lmayencourt/faboy/pcb/original.png

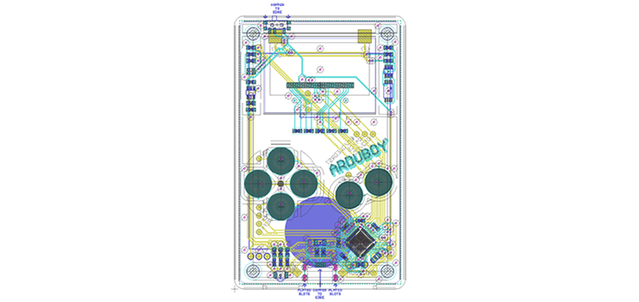
pcb/original.png
