lmayencourt/faboy/software/Qtboy/arduboy.png

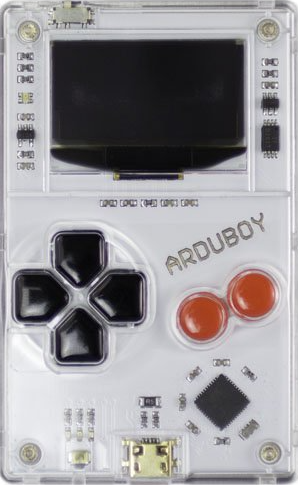
software/Qtboy/arduboy.png
