lmayencourt/faboy/software/game/ECOMD_AB_v10/ECOMD_AB_v10/Weapons.h

#ifndef WEAPONS_H
#define WEAPONS_H

#include <Arduino.h>

extern Arduboy arduboy;
extern SimpleButtons buttons;

#define POWERUP_MAXTIME     600
enum WEAPON_TYPE { DEFAULT_GUN = 0, SHOTGUN, MAGNUM, MACHINEGUN, FLAMETHROWER, DUAL_PISTOLS};
WEAPON_TYPE CURRENT_WEAPON;

PROGMEM const unsigned char guns[] = {
  // width, height
  16, 8,
  // tile 0
  0x00, 0x00, 0x00, 0x00, 0x7A, 0x7C, 0x2C, 0x1C, 0x0C, 0x0C,
  0x0C, 0x0C, 0x00, 0x00, 0x00, 0x00,
  // tile 1
  0x78, 0x78, 0x3A, 0x3C, 0x1C, 0x1C, 0x2C, 0x2C, 0x1C, 0x0C,
  0x0C, 0x1C, 0x1C, 0x1C, 0x1C, 0x0C,
  // tile 2
  0x00, 0xE0, 0xF0, 0x7A, 0x1C, 0x2E, 0x1A, 0x1A, 0x0E, 0x06,
  0x06, 0x06, 0x06, 0x06, 0x07, 0x00,
  // tile 3
  0x06, 0xCF, 0xFF, 0x3E, 0x2E, 0x1E, 0x0E, 0x0E, 0x1E, 0x7E,
  0xE6, 0x86, 0x06, 0x06, 0x07, 0x02,
  // tile 4
  0x62, 0x7A, 0x1E, 0x06, 0x0A, 0x06, 0x02, 0x02, 0xFA, 0xFE,
  0xFA, 0x02, 0x07, 0x07, 0x07, 0x07,
  // tile 5
  0x0C, 0x0C, 0x0C, 0x1C, 0x2C, 0x7C, 0x7A, 0x00, 0x00, 0x7A,
  0x7C, 0x2C, 0x1C, 0x0C, 0x0C, 0x0C,
};

PROGMEM const unsigned char bullets_is_mask[] = {
  // width, height
  16, 8,
  // frame 0
  0x04, 0x04, 0x00, 0x04, 0x00, 0x00, 0x00, 0x00, 0x00, 0x00,
  0x00, 0x00, 0x00, 0x00, 0x00, 0x00,
  // frame 1
  0x08, 0x00, 0x08, 0x14, 0x00, 0x00, 0x08, 0x00, 0x22, 0x00,
  0x08, 0x00, 0x00, 0x14, 0x00, 0x41,
  // frame 2
  0x04, 0x02, 0x04, 0x06, 0x00, 0x00, 0x00, 0x00, 0x00, 0x00,
  0x00, 0x00, 0x00, 0x00, 0x00, 0x00,
  // frame 3
  0x06, 0x06, 0x06, 0x00, 0x06, 0x00, 0x00, 0x00, 0x00, 0x00,
  0x00, 0x00, 0x00, 0x00, 0x00, 0x00,
  // frame 4
  0x08, 0x16, 0x11, 0x12, 0x0C, 0x00, 0x00, 0x00, 0x00, 0x00,
  0x00, 0x00, 0x00, 0x00, 0x00, 0x00,
  // frame 5
  0x04, 0x04, 0x04, 0x00, 0x00, 0x00, 0x00, 0x00, 0x00, 0x00,
  0x00, 0x00, 0x00, 0x00, 0x00, 0x00,
  // frame 6
  0x04, 0x00, 0x04, 0x04, 0x00, 0x00, 0x00, 0x00, 0x00, 0x00,
  0x00, 0x00, 0x00, 0x00, 0x00, 0x00,
  // frame 7
  0x41, 0x00, 0x14, 0x00, 0x00, 0x08, 0x00, 0x22, 0x00, 0x08,
  0x00, 0x00, 0x14, 0x08, 0x00, 0x08,
  // frame 8
  0x06, 0x04, 0x02, 0x04, 0x00, 0x00, 0x00, 0x00, 0x00, 0x00,
  0x00, 0x00, 0x00, 0x00, 0x00, 0x00,
  // frame 9
  0x06, 0x00, 0x06, 0x06, 0x06, 0x00, 0x00, 0x00, 0x00, 0x00,
  0x00, 0x00, 0x00, 0x00, 0x00, 0x00,
  // frame 10
  0x0C, 0x12, 0x11, 0x16, 0x08, 0x00, 0x00, 0x00, 0x00, 0x00,
  0x00, 0x00, 0x00, 0x00, 0x00, 0x00,
  // frame 11
  0x04, 0x04, 0x04, 0x00, 0x00, 0x00, 0x00, 0x00, 0x00, 0x00,
  0x00, 0x00, 0x00, 0x00, 0x00, 0x00,
};

class Bullet
{
  public:
    byte x;
    byte y;
    byte width = 4;
    byte height = 1;
    byte fuse = 0;
    byte xSpeed = 3;
    byte ySpeed = 0;
    byte damage = 1;
    boolean isActive = false;

    void Update() {
      if (isActive) {
        fuse--; if (fuse == 0) isActive = false;
        x += xSpeed;
        y += ySpeed;
      }
    }
};

class Weapons
{
  public:

    static const byte maxBullets = 6;
    int powerupTimer = POWERUP_MAXTIME;
    byte maxFuse = 23;
    byte fuse = 0;
    byte frameDelay = 1;
    byte maxCooldown =  3;
    byte kickBack = 0;
    byte cooldown = 0;
    byte currentBullet = 0;
    byte width = 4;
    byte height = 1;
    byte xSpeed = 3;
    byte xSpeedOffset = 0;
    byte yOffset = 0;
    byte ySpeed = 0;
    byte ySpeedOffset = 0;
    byte damage = 1;

    Bullet bullet[maxBullets];

    void shootDual()
    {
      currentBullet ++; if (currentBullet == maxBullets)currentBullet = 0;
      bullet[currentBullet].isActive = true;
      bullet[currentBullet].fuse =  maxFuse ;
      bullet[currentBullet].ySpeed = random(0, ySpeedOffset + 1);
      byte rand = random(0, 2); if (rand == 1) bullet[currentBullet].ySpeed *= -1;
    }
    boolean shoot()
    {
      if (cooldown == 0)
      {
        currentBullet ++; if (currentBullet == maxBullets)currentBullet = 0;
        bullet[currentBullet].isActive = true;
        bullet[currentBullet].fuse =  maxFuse ;
        bullet[currentBullet].ySpeed = random(0, ySpeedOffset + 1);
        byte rand = random(0, 2); if (rand == 1) bullet[currentBullet].ySpeed *= -1;

        cooldown = maxCooldown;
        return true;
      }
      else
      {
        return false;
      }
    }


    void Update()
    {

      //timer for weapons powerup (to avoid exploitation)
      powerupTimer --;
      
      if (cooldown > 0) cooldown --;

      for (byte i = 0; i < maxBullets; i++)
      {
        if (bullet[i].isActive)
        {
          bullet[i].Update();
        }
      }
    }

    void setBulletSpecs()
    {
      for (byte i = 0; i < maxBullets; i++)
      {
        bullet[i].width = width;
        bullet[i].height = height;
        bullet[i].xSpeed = xSpeed;
        bullet[i].ySpeed = ySpeed;
        bullet[i].damage = damage;
        bullet[i].isActive = false;
      }

    }

    void weaponSet(int weapType)
    {
      powerupTimer = POWERUP_MAXTIME;
      setBulletSpecs();
      switch (weapType) {
        case 0: //DEFAULT GUN
          frameDelay = 1;
          maxFuse = 30;
          fuse = 0;
          maxCooldown =  3;
          kickBack = 0;
          cooldown = 0;
          width = 4;
          height = 1;
          xSpeed = 3;
          xSpeedOffset = 0;
          yOffset = 0;
          ySpeed = 0;
          ySpeedOffset = 0;
          damage = 1;
          break;
        case 1: //SHOTGUN
          frameDelay = 1;
          maxFuse = 16;
          fuse = 0;
          maxCooldown =  40;
          kickBack = 8;
          cooldown = 0;
          width = 16;
          height = 7;
          xSpeed = 1;
          ySpeed = 0;
          yOffset = 0;
          ySpeedOffset = 0;
          damage = 5;
          break;
        case 2: //MAGNUM
          frameDelay = 1;
          maxFuse = 35;
          fuse = 0;
          maxCooldown =  20;
          kickBack = 4;
          cooldown = 0;
          width = 4;
          height = 2;
          xSpeed = 3;
          xSpeedOffset = 0;
          ySpeed = 0;
          yOffset = 0;
          ySpeedOffset = 0;
          damage = 2;
          break;
        case 3: //MACHINE_GUN:
          frameDelay = 1;
          maxFuse = 30;
          fuse = 0;
          maxCooldown =  8;
          kickBack = 5;
          cooldown = 0;
          width = 5;
          height = 2;
          xSpeed = 4;
          xSpeedOffset = 0;
          ySpeed = 0;
          yOffset = 1;
          ySpeedOffset = 0;
          damage = 1;
          break;
        case 4: //FLAMETHROWER:
          frameDelay = 3;
          maxFuse = 6;
          fuse = 0;
          maxCooldown =  4;
          cooldown = 0;
          kickBack = 0;
          width = 5;
          height = 5;
          xSpeed = 3;
          xSpeedOffset = 2;
          ySpeed = 0;
          yOffset = 1;
          ySpeedOffset = 1;
          damage = 2;
          break;
        case 5: //DUAL_PISTOLS:
          //SAME STATS AS DEFAULT_GUN
          frameDelay = 1;
          maxFuse = 30;
          fuse = 0;
          maxCooldown = 3;
          kickBack = 0;
          cooldown = 0;
          width = 3;
          height = 1;
          xSpeed = 3;
          xSpeedOffset = 0;
          yOffset = 0;
          ySpeed = 0;
          ySpeedOffset = 0;
          damage = 1;
          break;
      }
    }
};

Weapons weapon;

void makeShootingSounds() //pew pew sound
{
  switch (CURRENT_WEAPON)
  {
    case DEFAULT_GUN:
      arduboy.tunes.tone(100, 100);
      break;
    case SHOTGUN:
      arduboy.tunes.tone(140, 300);
      break;
    case MAGNUM:
      arduboy.tunes.tone(190, 300);
      break;
    case MACHINEGUN:
      arduboy.tunes.tone(120, 100);
      break;
    case FLAMETHROWER:
      arduboy.tunes.tone(100, 80);
      break;
    case DUAL_PISTOLS:
      arduboy.tunes.tone(100, 100);
      break;
  }
}

void shoot()
{
  if ((buttons.pressed(A_BUTTON) && CURRENT_WEAPON == MACHINEGUN)  || (buttons.pressed(A_BUTTON) && CURRENT_WEAPON == FLAMETHROWER) || buttons.justPressed(A_BUTTON))
  {
    //shoot normal bullets
    if (weapon.shoot()) {
      makeShootingSounds();
      byte yOffset = weapon.yOffset;
      byte randNum = random(0, 2); if (randNum == 1) yOffset *= -1;
      weapon.bullet[weapon.currentBullet].y = player.y + 2 + yOffset ;
      byte randxSpeedOffset = random(1, weapon.xSpeedOffset + 1);
      weapon.bullet[weapon.currentBullet].x = player.x + ((1 - (2 * playerFacing)) * 8);
      weapon.bullet[weapon.currentBullet].xSpeed =  ((1 - (2 * playerFacing)) * weapon.xSpeed) - ((1 - (2 * playerFacing)) * randxSpeedOffset);
      {
        for (byte i = 0; i <  weapon.kickBack; i++)
        {
          if (!checkCollisions()) player.x -= (1 - (2 * playerFacing));
        }
      }
      if (CURRENT_WEAPON == DUAL_PISTOLS)
      {
        weapon.shootDual();
        weapon.bullet[weapon.currentBullet].y = player.y + 3;
        weapon.bullet[weapon.currentBullet].x = player.x - ((-1 * playerFacing) * weapon.width);
        weapon.bullet[weapon.currentBullet].xSpeed = -  ((1 - (2 * playerFacing)) * weapon.xSpeed) + ((1 - (2 * playerFacing)));
      }
    }
  }
}

void updateWeapon()
{
  if (arduboy.everyXFrames(weapon.frameDelay))
  {
    weapon.Update();
    if (weapon.powerupTimer < 1)
    {
      CURRENT_WEAPON = DEFAULT_GUN;
      weapon.weaponSet(0);
    }
  }
}

void drawBullets()
{
  for (byte i = 0; i < weapon.maxBullets; i++)
  {
    if (weapon.bullet[i].isActive)  sprites.drawSelfMasked(weapon.bullet[i].x, weapon.bullet[i].y, bullets_is_mask, CURRENT_WEAPON + (playerFacing * 6));
  }
}

#endif
