lmayencourt/faboy/software/Faboy/src/core/core.cpp

#include "core.h"

// need to redeclare these here since we declare them static in .h
volatile uint8_t *ArduboyCore::mosiport, 
  *ArduboyCore::csport, *ArduboyCore::dcport;
uint8_t ArduboyCore::mosipinmask, 
  ArduboyCore::cspinmask, ArduboyCore::dcpinmask;

const uint8_t PROGMEM pinBootProgram[] = {
  // buttons
  PIN_LEFT_BUTTON, INPUT_PULLUP,
  PIN_RIGHT_BUTTON, INPUT_PULLUP,
  PIN_UP_BUTTON, INPUT_PULLUP,
  PIN_DOWN_BUTTON, INPUT_PULLUP,
  PIN_A_BUTTON, INPUT_PULLUP,
  PIN_B_BUTTON, INPUT_PULLUP,

  // OLED SPI
  DC, OUTPUT,
  CS, OUTPUT,
  RST, OUTPUT,
  0
};

const uint8_t PROGMEM lcdBootProgram[] = {
  // boot defaults are commented out but left here incase they
  // might prove useful for reference
  //
  // Further reading: https://www.adafruit.com/datasheets/SSD1306.pdf
  //
  // Display Off
  // 0xAE,     

  // Set Display Clock Divisor v = 0xF0
  // default is 0x80
  0xD5, 0xF0,

  // Set Multiplex Ratio v = 0x3F
  // 0xA8, 0x3F,   

  // Set Display Offset v = 0
  // 0xD3, 0x00, 

  // Set Start Line (0)
  // 0x40,     

  // Charge Pump Setting v = enable (0x14)
  // default is disabled
  0x8D, 0x14,   

  // Set Segment Re-map (A0) | (b0001)
  // default is (b0000)
  0xA1,     

  // Set COM Output Scan Direction
  0xC8,     

  // Set COM Pins v
  // 0xDA, 0x12,   

  // Set Contrast v = 0xCF
  0x81, 0xCF,   

  // Set Precharge = 0xF1
  0xD9, 0xF1,
    
  // Set VCom Detect
  // 0xDB, 0x40,   

  // Entire Display ON
  // 0xA4,     

  // Set normal/inverse display
  // 0xA6,  

  // Display On
  0xAF,     

  // set display mode = horizontal addressing mode (0x00)
  0x20, 0x00,  

  // set col address range 
  // 0x21, 0x00, COLUMN_ADDRESS_END,

  // set page address range
  // 0x22, 0x00, PAGE_ADDRESS_END
};


ArduboyCore::ArduboyCore() {}

void ArduboyCore::boot()
{
  #if F_CPU == 8000000L
  slowCPU();
  #endif

  SPI.begin();
  bootPins();
  bootLCD();

  #ifdef SAFE_MODE
  if (buttonsState() == (LEFT_BUTTON | UP_BUTTON))
    safeMode();
  #endif

  saveMuchPower();
}

#if F_CPU == 8000000L
// if we're compiling for 8Mhz we need to slow the CPU down because the
// hardware clock on the Arduboy is 16MHz
void ArduboyCore::slowCPU()
{
  uint8_t oldSREG = SREG;
  cli();                // suspend interrupts
  CLKPR = _BV(CLKPCE);  // allow reprogramming clock
  CLKPR = 1;            // set clock divisor to 2 (0b0001)
  SREG = oldSREG;       // restore interrupts
}
#endif

void ArduboyCore::bootPins()
{
  uint8_t pin, mode;
  const uint8_t *i = pinBootProgram;

  while(true) {
    pin = pgm_read_byte(i++);
    mode = pgm_read_byte(i++);
    if (pin==0) break;
    pinMode(pin, mode);
  }

  digitalWrite(RST, HIGH);
  delay(1);           // VDD (3.3V) goes high at start, lets just chill for a ms
  digitalWrite(RST, LOW);   // bring reset low
  delay(10);          // wait 10ms
  digitalWrite(RST, HIGH);  // bring out of reset
}

void ArduboyCore::bootLCD()
{
  // setup the ports we need to talk to the OLED
 // csport = portOutputRegister(digitalPinToPort(CS));
 // cspinmask = digitalPinToBitMask(CS);
 // dcport = portOutputRegister(digitalPinToPort(DC));
 // dcpinmask = digitalPinToBitMask(DC);
  pinMode(DC, OUTPUT);
  pinMode(CS, OUTPUT);

  SPI.setClockDivider(SPI_CLOCK_DIV2);

  LCDCommandMode();
  // run our customized boot-up command sequence against the
  // OLED to initialize it properly for Arduboy
  for (int8_t i=0; i < sizeof(lcdBootProgram); i++) {
    SPI.transfer(pgm_read_byte(lcdBootProgram + i));
  }
  LCDDataMode();
}

void ArduboyCore::LCDDataMode()
{
  //*dcport |= dcpinmask; // dc 1
  //*csport &= ~cspinmask;  // cs c0
  digitalWrite(DC, HIGH);
  digitalWrite(CS,LOW);

}

void ArduboyCore::LCDCommandMode()
{
 // *csport |= cspinmask;  
 // *dcport &= ~dcpinmask;
 // *csport &= ~cspinmask;

  digitalWrite(CS, HIGH);
  digitalWrite(DC, LOW);
  digitalWrite(CS, LOW);
}



void ArduboyCore::safeMode()
{
  blank(); // too avoid random gibberish
  while (true) {
    asm volatile("nop \n");
  }
}


/* Power Management */

void ArduboyCore::idle()
{
  set_sleep_mode(SLEEP_MODE_IDLE);
  sleep_mode();
}

void ArduboyCore::saveMuchPower()
{
  power_adc_disable();
  power_usart0_disable();
  power_twi_disable();
  // timer 0 is for millis()
  // timers 1 and 3 are for music and sounds
  power_timer2_disable();
  power_usart1_disable();
  // we need USB, for now (to allow triggered reboots to reprogram)
  // power_usb_disable()
}

uint8_t ArduboyCore::width() { return WIDTH; }

uint8_t ArduboyCore::height() { return HEIGHT; }


/* Drawing */

void ArduboyCore::paint8Pixels(uint8_t pixels)
{
  SPI.transfer(pixels);
}

void ArduboyCore::paintScreen(const unsigned char *image)
{
  for (int i = 0; i < (HEIGHT*WIDTH)/8; i++)
  {
    SPI.transfer(pgm_read_byte(image + i));
  }
}

// paint from a memory buffer, this should be FAST as it's likely what
// will be used by any buffer based subclass
void ArduboyCore::paintScreen(unsigned char image[])
{
  uint8_t c;
  int i = 0;

  SPDR = image[i++]; // set the first SPI data byte to get things started

  // the code to iterate the loop and get the next byte from the buffer is
  // executed while the previous byte is being sent out by the SPI controller
  while (i < (HEIGHT * WIDTH) / 8)
  {
    // get the next byte. It's put in a local variable so it can be sent as
    // as soon as possible after the sending of the previous byte has completed
    c = image[i++];

    while (!(SPSR & _BV(SPIF))) { } // wait for the previous byte to be sent

    // put the next byte in the SPI data register. The SPI controller will
    // clock it out while the loop continues and gets the next byte ready
    SPDR = c;
  }
  while (!(SPSR & _BV(SPIF))) { } // wait for the last byte to be sent
}

void ArduboyCore::blank()
{
  for (int i = 0; i < (HEIGHT*WIDTH)/8; i++)
    SPI.transfer(0x00);
}

void ArduboyCore::sendLCDCommand(uint8_t command)
{
  LCDCommandMode();
  SPI.transfer(command);
  LCDDataMode();
}

// invert the display or set to normal
// when inverted, a pixel set to 0 will be on
void ArduboyCore::invert(boolean inverse)
{
  sendLCDCommand(inverse ? OLED_PIXELS_INVERTED : OLED_PIXELS_NORMAL);
}

// turn all display pixels on, ignoring buffer contents
// or set to normal buffer display
void ArduboyCore::allPixelsOn(boolean on)
{
  sendLCDCommand(on ? OLED_ALL_PIXELS_ON : OLED_PIXELS_FROM_RAM);
}

// flip the display vertically or set to normal
void ArduboyCore::flipVertical(boolean flipped)
{
  sendLCDCommand(flipped ? OLED_VERTICAL_FLIPPED : OLED_VERTICAL_NORMAL);
}

#define OLED_HORIZ_FLIPPED 0xA0 // reversed segment re-map
#define OLED_HORIZ_NORMAL 0xA1 // normal segment re-map

// flip the display horizontally or set to normal
void ArduboyCore::flipHorizontal(boolean flipped)
{
  sendLCDCommand(flipped ? OLED_HORIZ_FLIPPED : OLED_HORIZ_NORMAL);
}

/* RGB LED */

void ArduboyCore::setRGBled(uint8_t red, uint8_t green, uint8_t blue)
{
#ifdef ARDUBOY_10 // RGB, all the pretty colors
  // inversion is necessary because these are common annode LEDs
  analogWrite(RED_LED, 255 - red);
  analogWrite(GREEN_LED, 255 - green);
  analogWrite(BLUE_LED, 255 - blue);
#elif defined(FABOY_DEV) // RGB, all the pretty colors
  // inversion is necessary because these are common annode LEDs
  analogWrite(RED_LED, 255 - red);
  analogWrite(GREEN_LED, 255 - green);
  analogWrite(BLUE_LED, 255 - blue);
#elif defined(AB_DEVKIT)
  // only blue on devkit
  digitalWrite(BLUE_LED, ~blue);
#endif
}

/* Buttons */

uint8_t ArduboyCore::getInput()
{
  return buttonsState();
}


uint8_t ArduboyCore::buttonsState()
{
  uint8_t buttons;
  
  // using ports here is ~100 bytes smaller than digitalRead()
#ifdef AB_DEVKIT
  // down, left, up
  buttons = ((~PINB) & B01110000);
  // right button
  buttons = buttons | (((~PINC) & B01000000) >> 4);
  // A and B
  buttons = buttons | (((~PINF) & B11000000) >> 6);
#elif defined(ARDUBOY_10)
  // down, up, left right
  buttons = ((~PINF) & B11110000);
  // A (left)
  buttons = buttons | (((~PINE) & B01000000) >> 3);
  // B (right)
  buttons = buttons | (((~PINB) & B00010000) >> 2);
  #elif defined(FABOY_DEV)
  // down, up, left right
  buttons = ((~PINF) & B00110011);
  // A (left), B(right)
  buttons = buttons | (((~PIND) & B00001100) );
#endif
  
  return buttons;
}
