lmayencourt/faboy/software/game/ECOMD_AB_v10/ECOMD_AB_v10/background.h

#ifndef BACKGROUND_H
#define BACKGROUND_H

byte fireFrame = 0;

PROGMEM const unsigned char surrounding_plus_mask[] = {
  // width, height
  8, 8,
  // tile 0
  0x00, 0x00, 0x00, 0x00, 0x00, 0x00, 0x00, 0x00, 0x00, 0x00,
  0x00, 0x00, 0x00, 0x00, 0x00, 0x00,
  // tile 1
  0xFF, 0xFF, 0xAA, 0xFF, 0x53, 0xFF, 0x02, 0xFF, 0x53, 0xFF,
  0x02, 0xFF, 0xFF, 0xFF, 0xFE, 0xFF,
  // tile 2
  0x03, 0x03, 0xF2, 0xF3, 0x13, 0xF3, 0x1E, 0xFF, 0x13, 0xF3,
  0x12, 0xF3, 0x13, 0xF3, 0x12, 0xF3,
  // tile 3
  0x13, 0xF3, 0x12, 0xF3, 0x13, 0xF3, 0x12, 0xF3, 0x13, 0xF3,
  0x12, 0xF3, 0x13, 0xF3, 0x12, 0xF3,
  // tile 4
  0x13, 0xF3, 0x12, 0xF3, 0x13, 0xF3, 0x1E, 0xFF, 0x13, 0xF3,
  0xF2, 0xF3, 0x03, 0x03, 0x02, 0x03,
  // tile 5
  0x03, 0x03, 0x02, 0x03, 0x03, 0x03, 0x02, 0x03, 0x03, 0x03,
  0x02, 0x03, 0x03, 0x03, 0x02, 0x03,
  // tile 6
  0x03, 0x03, 0x02, 0x03, 0xFF, 0xFF, 0x02, 0x03, 0x03, 0x03,
  0x02, 0x03, 0x03, 0x03, 0x02, 0x03,
  // tile 7
  0x03, 0x03, 0x02, 0x03, 0x03, 0x03, 0x02, 0x03, 0x03, 0x03,
  0x02, 0x03, 0xFF, 0xFF, 0x02, 0x03,
  // tile 8
  0xF3, 0xF3, 0x12, 0xF3, 0x1F, 0xFF, 0x12, 0xF3, 0x13, 0xF3,
  0x12, 0xF3, 0x13, 0xF3, 0x12, 0xF3,
  // tile 9
  0x13, 0xF3, 0x12, 0xF3, 0x13, 0xF3, 0x12, 0xF3, 0x1F, 0xFF,
  0x12, 0xF3, 0xF3, 0xF3, 0x02, 0x03,
  // tile 10
  0xFF, 0xFF, 0xAA, 0xFF, 0x00, 0xFF, 0x00, 0xFF, 0x00, 0xFF,
  0x00, 0xFF, 0xFF, 0xFF, 0xFF, 0xFF,
  // tile 11
  0xFF, 0xFF, 0xAA, 0xFF, 0x94, 0xFF, 0x80, 0xFF, 0x94, 0xFF,
  0x80, 0xFF, 0xFF, 0xFF, 0xFF, 0xFF,
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
0x00, 0x00, 0x00, 0x00, 0x00, 0x00, 0x80, 0x80, 0x00, 0x00, 0x00, 0x00, 0xE0, 0xE0, 0xC0, 0xC0, 
0x00, 0x00, 0x00, 0x00, 0x78, 0x78, 0xFE, 0xFE, 0xFC, 0xFC, 0x9E, 0xFE, 0xEF, 0xFF, 0xF1, 0xFF, 
0xFB, 0xFF, 0xF6, 0xFE, 0xEF, 0xFF, 0xF7, 0xFF, 0xCF, 0xFF, 0xFE, 0xFE, 0x7C, 0x7C, 0x01, 0x01, 

};


PROGMEM const byte backdrop_tiles[] =
{
  0,  0,  0,  0,  0,  0,  0,  0,  0,  0,  0,  0,  0, 14,  3,  8,  0,  0,  0,  0,
  0,  0,  7,  3,  7,  0,  0,  0,  0, 14, 15,  0,  0,  3,  3,  3,  0,  0,  0, 13,
  0,  4,  8,  3,  9, 10, 10, 13,  0,  3,  1, 13,  0,  3,  3,  3,  0,  7,  0,  2,
  1,  5,  3,  3,  3,  1,  1, 12, 11,  3,  3,  2, 10,  3,  3,  3,  5,  2,  0,  2,
  2,  6,  3,  3,  3, 11,  1,  3,  3,  3,  3,  2, 11,  3,  3,  3,  3,  3, 11,  2,
  3,  3,  3,  3,  3,  3,  3,  3,  3,  3,  3,  3,  3,  3,  3,  3,  3,  3,  3,  3,
};

void drawSurrounding()
{
  for (byte y = 0; y < 8; y++)
  {
    for (byte x = 0; x < 16; x++)
    {
      sprites.drawPlusMask(x * 8, y * 8, surrounding_plus_mask, pgm_read_byte(&surrounding_tiles[x + 16 * y]));
    }
  }
}

void drawBackDrop()
{
  for (byte y = 0; y < 6; y++)
  {
    for (byte x = 0; x < 20; x++)
    {
      sprites.drawPlusMask((x * 8) + 8 - (player.x / 4) , 16 + y * 8, backdrop_plus_mask, pgm_read_byte(&backdrop_tiles[x + 20 * y]));
    }
  }
}

void drawFirePit()
{
  if (arduboy.everyXFrames(2))fireFrame++;
  if (fireFrame > 14)fireFrame = 0;
  sprites.drawPlusMask(56, 48, firepit_plus_mask, fireFrame);
}
#endif
