lmayencourt/faboy/software/game/ECOMD_AB_v10/ECOMD_AB_v10/menu_bitmap.h

// TEAM-arg07b.png  width: 128 height: 48
const uint8_t PROGMEM TEAMarg2[] = {
0x7f,0x2f,0x30,0x68,0xb7,0xdb,0xed,0xdb,0x53,0x9f,0xfa,0x73,0x97,0xbb,0xd5,0xe7,
0x2e,0x77,0xb9,0xcb,0x5d,0x6e,0xbb,0xbd,0xdc,0xe5,0x2e,0x77,0xb9,0xcb,0x5d,0xee,
0x72,0x97,0x5b,0x2b,0xbb,0xdc,0x6e,0xb7,0xdb,0xed,0x76,0xbb,0xdd,0x6e,0xb7,0xdb,
0xed,0x76,0xbb,0xdd,0x6e,0xb7,0xca,0xae,0x43,0x57,0x76,0xbb,0x5d,0x6e,0xb7,0xdb,
0xed,0x76,0xbb,0xdd,0x6e,0xb7,0xdb,0xad,0xb2,0xdb,0x75,0xd8,0x5a,0x2a,0xb9,0xdd,
0x6e,0xb7,0xeb,0x75,0x74,0xd9,0xe5,0x72,0xf9,0xfd,0xdf,0xea,0x72,0x57,0x77,0x75,
0x97,0x3b,0x6d,0x95,0x93,0xca,0x2a,0xbb,0x0e,0xbf,0x6d,0x6f,0x75,0xab,0xed,0xb9,
0x5c,0x77,0x2a,0xcf,0x9f,0x76,0xda,0xd5,0xad,0x4e,0xf7,0xaa,0x57,0xe9,0x74,0x3a,
0x9d,0xbb,0xa4,0xc2,0xd1,0x76,0xb6,0xb4,0xd3,0x2e,0x9f,0x5e,0x5a,0x85,0xbc,0x74,
0x3a,0x9d,0x4e,0xa7,0x3b,0x67,0x57,0x5b,0xaf,0x93,0x4a,0xb9,0x9d,0x52,0xca,0x2d,
0x97,0xdb,0x74,0x6c,0x49,0xe5,0x9c,0x92,0x4a,0x2a,0xa9,0xa4,0x53,0x84,0xe9,0xf4,
0xea,0x53,0xbf,0x56,0x2a,0x65,0xed,0x6e,0xa7,0x94,0x52,0x4a,0x46,0x9f,0x5e,0xaf,
0x97,0xcb,0x6d,0xbc,0x4b,0xe7,0x5c,0xff,0x13,0x7a,0x9f,0xde,0xce,0xbe,0xd6,0xb9,
0xee,0xd4,0xae,0x3b,0xb5,0x6e,0x7b,0xab,0x5b,0x8d,0x24,0x25,0x4b,0x29,0x95,0x4a,
0x76,0x56,0x3a,0x1d,0xdb,0xce,0xcd,0x96,0x4e,0xa7,0xd3,0xe9,0xec,0x4e,0x4a,0xe9,
0xec,0x08,0xdb,0x3a,0x67,0xe7,0x52,0xb3,0x29,0x2d,0xf5,0xa8,0x4b,0xa7,0xd3,0xe9,
0x74,0xce,0xb9,0x5b,0x2f,0xdd,0x6a,0x87,0xac,0xa4,0x2a,0x25,0x95,0x54,0x52,0x49,
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
0x39,0xa9,0xf0,0xe8,0xf9,0x76,0x4e,0x75,0xce,0xa9,0xb4,0xbc,0x73,0xf2,0xae,0x96,
0x57,0xa5,0xaa,0x5a,0x9e,0x4e,0xa7,0xd3,0x4c,0xd2,0xb9,0x4b,0x2a,0xa9,0xa4,0x92,
0xca,0x6e,0xb7,0xdb,0xd0,0x99,0xb7,0x3e,0x34,0x66,0xd3,0xbb,0x4a,0x3a,0x9b,0x8f,
0x2e,0x7c,0xc5,0xd5,0x56,0x55,0xe5,0x94,0xba,0x5c,0xaf,0x2e,0x77,0xab,0xcb,0x49,
0x75,0x39,0xab,0xaa,0xda,0xaa,0x70,0xb7,0xde,0x2a,0xa9,0xa4,0x92,0xca,0x39,0x55,
0x4a,0x49,0x55,0x6a,0xab,0x4a,0x39,0x27,0x95,0x73,0x52,0x49,0xe7,0xe4,0x56,0xa9,
0x72,0x97,0xbb,0xdc,0xad,0x5c,0x27,0x63,0x5d,0x3a,0xe7,0x3a,0x97,0xea,0x9d,0x93,
0x4a,0x2a,0xa9,0xa4,0x72,0xce,0x71,0xd1,0xd9,0xab,0xda,0xae,0x6a,0xb9,0x54,0x72,
0xa9,0xe4,0x36,0x5f,0xb9,0xaa,0xea,0xaa,0xba,0xaa,0xae,0xaa,0xab,0xea,0xaa,0xca,
0x55,0xb6,0xb2,0x21,0x30,0x9d,0x4e,0xa7,0xd3,0xdb,0xed,0x76,0xab,0xa4,0xe2,0x92,
0x8a,0x34,0x45,0x54,0x55,0x11,0xc5,0xb5,0x8e,0x38,0xba,0x8a,0xac,0xaa,0x22,0xaa,
0x92,0xc1,0x63,0x9f,0x4a,0x11,0x55,0x55,0x7e,0xae,0xf5,0xbc,0xd1,0x55,0x64,0x55,
0x95,0xbf,0x72,0x63,0x2d,0xbf,0x2c,0xa5,0xa4,0x52,0xa5,0xa4,0x52,0xa5,0xa4,0x4a,
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
};
