lmayencourt/faboy/software/game/SHRUN-AB_v15/SHRUN-AB_v15/otherbitmaps.h

const unsigned char PROGMEM TEAMarg2[] = //128,48
{
  //         ########                                                                                       ########                 
  //         ###########                                                                                   ##      ##                
  //         ####    ##################                                                                   ##  #### ###               
  //         #### ##    ################ ####################           #############         ######     ##  ##  # ####              
  //         #### #####                #######################       ##################      ########   ##  ###  # #####             
  //         #### ##  ######  ######## ##                   ###     ####            ####     ##     ## ##  ####### #  ###            
  // ####### ####  #  ####### #####  #  # #################  ##    ###   ##########   ###   ##  ###  ###  ###  ### #   ### ##########
  //         ##### ##########  ####  ## #  ################# ##   ###  ##############   ##  ## #####  #  ###    ## ##  ###           
  //         ##### ########### ######## #   ################  #   ##  #################  ####  ######   ####    ## ########          
  // ##### # #####             ########     ################# #  ##  #######    ######## #### ######## ######  ### ########  # # ####
  // #  #    ###### ####################    ################# #  ## #######      #######  ##  #################### ########      #  #
  // #  # #  ###### ####################     #######          # ##  ######       ####  ## ## #################  ## ######## # #  #  #
  // ####    ######  #  ################     ##############   # ## #######       ####  ## #  #################  ## ########      ####
  // ####  # ####### #  #################  # ##############   ###  ######       ######### # ###################### ########  # # ####
  // ####    ####### ####################  # ###############  ### #######       ########    #####################  ########      ####
  // #### #   ######        #########      # ###############  ##  ######       #########   ###################### ######### # #  ####
  // ####     #####          ########     ##  ############## ### ######################    ###################### #########     #####
  // ##### #  #####          #########    ### ########        #  ######################   ####################### ########   #  #####
  // #####     ###            ########    ### ###############   ######################    ####################### ########      #####
  // ###### #  ###         #  #########  #### ################  #######      #########   ######## ############### ########  # # #####
  // ######    ##          #   ########  ####  ################  ######      ########    #######  ############### ########      #####
  // ####### #  #         ###  ######### ##### ################# #####       ########   ########   ###### ####### ######## # # ######
  // #######    #         ###   ########  #### #  ############## #####      ########    #######    #####  ####### ########     ######
  // ######## # ######## #####  ##  ##### #### #  ########                  ###  ###    #######     ###   ######  ########  #  ######
  // ########          # #####   #  ##### #### #####             #         ####  ##                 ##    ###  # #########     ######
  // #  ###### # # # # ########  #####    ####                ## #         ########           ##          ###  # ######### # # ###  #
  // #  ######          #######           ####                ## #     ###                     #            #### #########     ###  #
  // ########## # # # # #########         # ##                   #     ###             ##      ##             ## #########  # #######
  //                    ########         ## ##                   #    ####             ##       #                ########            
  //         ###         #######         #  ##              ######    ####            ####      ##  #    #       ########            
  // ######### ######    ######         ##   #       #####################            # ##       #  ##  ####      #######   #########
  //       ##   ##       ######         #    ################            ############## ######################     ######            
  //      ##     ##   ## #####         ## ## #########                   ############    #######################    #####            
  //     ## ##    ##  ##  ####         #  ##                                                  ##     #############   #### ##         
  //     #  ##     #      ###         ##          ########    ##########      #########       ##     ##### #########  ### ##         
  //     ##       ##      ###     #####          ##########   ###########    ###########           ######      ##########            
  //      ##   # ##       #############         ############  ############   ###########          ####            #######   ###      
  //       ##   ##   ###  ########  ####        ############  #####  #####  #####   ####       ## ####    ###               # #      
  //        ## ##    # #            ####        #####   ####  #####   ####  ####               ##  ##     # #               ###      
  //         ###     ###             ##         #####   ####  #####   ###   ####   ######                 ###                        
  //                                            ############  ##########    #####  ######                                            
  //                                            ###########      ########      ########                                              
  //                                            ########### #### ## ##### #### ######## ####                                         
  //                                            #####   ### #  # ##  #### #  # ######## #  #                                         
  //                                            #####   ### #### ##   ### #### ######## ####                                         
  //                                                                                                                                 
  //                                                                                                                                 
  //                                                                                                                                 
  0x40, 0x40, 0x40, 0x40, 0x40, 0x40, 0x40, 0x00, 0xFF, 0xFF, 0xFF, 0xFF, 0x83, 0x3B, 0xFB, 0x93, 0x96, 0xF6, 0xE6, 0xEC, 0xEC, 0xEC, 0xEC, 0xCC, 0x0C, 0x6C, 0xEC, 0xEC, 0xEC, 0xEC, 0x2C, 0x2C, 0xEC, 0x8C, 0x38, 0xF0, 0x18, 0x58, 0xD8, 0xD8, 0xD8, 0xD8, 0xD8, 0xD8, 0xD8, 0xD8, 0xD8, 0xD8, 0xD8, 0xD8, 0xD8, 0xD8, 0xD8, 0xD8, 0x98, 0x38, 0xF0, 0xE0, 0x00, 0x00, 0x00, 0x80, 0xC0, 0xE0, 0x70, 0x30, 0xB0, 0x98, 0xD8, 0xD8, 0xD8, 0xD8, 0xD8, 0xD8, 0xD8, 0xD8, 0xD8, 0xD8, 0x98, 0xB8, 0x30, 0x70, 0x60, 0xC0, 0x80, 0x00, 0x00, 0xC0, 0xF0, 0x38, 0x98, 0xD8, 0xD8, 0xD8, 0x98, 0x30, 0x60, 0xC0, 0x60, 0x30, 0x98, 0xCC, 0xE6, 0x73, 0x39, 0x3D, 0x65, 0xE5, 0xFD, 0x01, 0xFF, 0x9E, 0x1C, 0x38, 0xF0, 0xE0, 0xC0, 0x00, 0x40, 0x40, 0x40, 0x40, 0x40, 0x40, 0x40, 0x40, 0x40, 0x40, 
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
};

const unsigned char PROGMEM spotlight_bitmap[] =
{
  //                                 
  //                                 
  //             ########            
  //           ############          
  //         ################        
  //        ##################       
  //       ####################      
  //      ######################     
  //     ########################    
  //     ########################    
  //    ##########################   
  //    ##########################   
  //   ############################  
  //   ############################  
  //   ############################  
  //   ############################  
  //   ############################  
  //   ############################  
  //   ############################  
  //   ############################  
  //    ##########################   
  //    ##########################   
  //     ########################    
  //     ########################    
  //      ######################     
  //       ####################      
  //        ##################       
  //         ################        
  //           ############          
  //             ########            
  //                                 
  //                                 
  0x00, 0x00, 0x00, 0x00, 0x00, 0x80, 0xC0, 0xE0, 0xF0, 0xF0, 0xF8, 0xF8, 0xFC, 0xFC, 0xFC, 0xFC, 0xFC, 0xFC, 0xFC, 0xFC, 0xF8, 0xF8, 0xF0, 0xF0, 0xE0, 0xC0, 0x80, 0x00, 0x00, 0x00, 0x00, 0x00, 
  0x00, 0x00, 0xF0, 0xFC, 0xFF, 0xFF, 0xFF, 0xFF, 0xFF, 0xFF, 0xFF, 0xFF, 0xFF, 0xFF, 0xFF, 0xFF, 0xFF, 0xFF, 0xFF, 0xFF, 0xFF, 0xFF, 0xFF, 0xFF, 0xFF, 0xFF, 0xFF, 0xFF, 0xFC, 0xF0, 0x00, 0x00, 
  0x00, 0x00, 0x0F, 0x3F, 0xFF, 0xFF, 0xFF, 0xFF, 0xFF, 0xFF, 0xFF, 0xFF, 0xFF, 0xFF, 0xFF, 0xFF, 0xFF, 0xFF, 0xFF, 0xFF, 0xFF, 0xFF, 0xFF, 0xFF, 0xFF, 0xFF, 0xFF, 0xFF, 0x3F, 0x0F, 0x00, 0x00, 
  0x00, 0x00, 0x00, 0x00, 0x00, 0x01, 0x03, 0x07, 0x0F, 0x0F, 0x1F, 0x1F, 0x3F, 0x3F, 0x3F, 0x3F, 0x3F, 0x3F, 0x3F, 0x3F, 0x1F, 0x1F, 0x0F, 0x0F, 0x07, 0x03, 0x01, 0x00, 0x00, 0x00, 0x00, 0x00, 
};

const unsigned char PROGMEM shadowRunner_bitmap[] =
{
  //     # #     # #   # #       # # #       # # # # #               # # #         # #   # #   # #
  //    # # #   # #     # #     # # # #       # # # # # #         # # # # #       # #   # #     # #
  //   # # #     # #   # #     # # # # #     # # # # # # #       # # # # # #       # #   # #   # #
  //  # # # #   # #     # #   # # # # # #     # # # # # # #     # # # # # # #     # #   # #     # #
  //   # #       # #   # #     # #     # #   # #       # #       # #     # # #     # #   # #   # #
  //  # # #     # #     # #   # #     # #     # #       # #     # #       # # #   # #   # #     # #
  //   # #       # # # # #     # #     # #   # #         # #   # #         # #     # #   # #   # #
  //  # # #     # # # # # #   # #     # #     # #       # #     # #         # #   # #   # #     # #
  //   # # #     # # # # #     # # # # # #   # #         # #   # #         # #     # #   # #   # #
  //    # # #   # # # # # #   # # # # # #     # #       # #     # #         # #   # #   # #     # #
  //     # #     # #   # #     # # # # # #   # #       # # #   # # #       # #     # #   # #   # #
  //    # # #   # #     # #   # # #   # #     # # # # # # #     # # #     # #     # #   # #     # #
  // # # # #     # #   # #     # #           #           #       # #         #       #         # #
  //  # # #     # #     # #   # #    ######   # ###  ###    ####  #   #####    #####   ######   # #
  // # # #       # #   # #     # #   #######    ###  ###   ######    #######  ###### # #######   #
  //  # #       # #     # #   # #    ######## # ###  ###  ########  ########  ######   ########
  //                                 ###  ###   ###  ###  ###  ###  ###  ###  ###      ###  ###
  //                                 ###  ###   ###  ###  ###  ###  ###  ###  ######   ###  ###
  //                                 ### ####   ###  ###  ###  ###  ###  ###  ######   ### ####
  //                                 ### ###    ###  ###  ###  ###  ###  ###  ######   ### ###
  //                                 ### ###    ###  ###  ###  ###  ###  ###  ###      ### ###
  //                                 ### ####   ########  ###  ###  ###  ###  ######   ### ####
  //                                 ###  ###    ######   ###  ###  ###  ###  ######   ###  ###
  //
  0x00, 0xA8, 0x54, 0xAA, 0x55, 0xAA, 0x05, 0x0A, 0x00, 0x00, 0x00, 0xAA, 0x55, 0xAA, 0x55, 0x80, 0x40, 0x80, 0x55, 0xAA, 0x55, 0xAA, 0x00, 0x00, 0x00, 0xA8, 0x54, 0xAA, 0x55, 0x0A, 0x05, 0x0A, 0x05, 0xAA, 0x54, 0xA8, 0x50, 0x00, 0x00, 0x00, 0x55, 0xAA, 0x55, 0xAA, 0x05, 0x0A, 0x05, 0x0A, 0x05, 0x0A, 0x14, 0xAA, 0x54, 0xA8, 0x40, 0x00, 0x00, 0x00, 0x40, 0xA8, 0x54, 0xAA, 0x14, 0x0A, 0x05, 0x0A, 0x05, 0x0A, 0x15, 0x2A, 0x54, 0xA8, 0x50, 0xA0, 0x00, 0x00, 0x00, 0xAA, 0x55, 0xAA, 0x55, 0x00, 0x00, 0xAA, 0x55, 0xAA, 0x55, 0x00, 0x00, 0x00, 0x55, 0xAA, 0x55, 0xAA,
  0x50, 0xA0, 0x51, 0xAA, 0x55, 0x2A, 0x15, 0x0A, 0x00, 0x00, 0x00, 0xAA, 0x55, 0xAA, 0x55, 0x02, 0x01, 0x02, 0x55, 0xAA, 0x55, 0xAA, 0x00, 0x00, 0x00, 0xAA, 0x55, 0xAA, 0x55, 0x0A, 0x05, 0x02, 0xE5, 0xEA, 0xE5, 0xEA, 0xE5, 0xE0, 0xC0, 0x80, 0x15, 0xAA, 0x05, 0xEA, 0xE0, 0xE8, 0x00, 0x08, 0xE0, 0xE8, 0xE4, 0x0A, 0x15, 0x8A, 0xC5, 0xE0, 0xE0, 0xE0, 0xE5, 0xCA, 0x95, 0x2A, 0x14, 0x88, 0xC0, 0xE0, 0xE0, 0xE0, 0xE0, 0xE8, 0xC5, 0x0A, 0x15, 0xC2, 0xE0, 0xE0, 0xE0, 0xEA, 0xE5, 0x0A, 0x55, 0x00, 0xE0, 0xEA, 0xE5, 0xEA, 0xE5, 0xE0, 0xC0, 0x80, 0x15, 0x2A, 0x55, 0x2A,
  0x00, 0x00, 0x00, 0x00, 0x00, 0x00, 0x00, 0x00, 0x00, 0x00, 0x00, 0x00, 0x00, 0x00, 0x00, 0x00, 0x00, 0x00, 0x00, 0x00, 0x00, 0x00, 0x00, 0x00, 0x00, 0x00, 0x00, 0x00, 0x00, 0x00, 0x00, 0x00, 0x7F, 0x7F, 0x7F, 0x00, 0x3C, 0x7F, 0x7F, 0x67, 0x00, 0x00, 0x00, 0x3F, 0x7F, 0x7F, 0x60, 0x60, 0x7F, 0x7F, 0x3F, 0x00, 0x00, 0x7F, 0x7F, 0x7F, 0x00, 0x00, 0x7F, 0x7F, 0x7F, 0x00, 0x00, 0x7F, 0x7F, 0x7F, 0x00, 0x00, 0x7F, 0x7F, 0x7F, 0x00, 0x00, 0x7F, 0x7F, 0x7F, 0x6E, 0x6E, 0x6E, 0x00, 0x00, 0x00, 0x7F, 0x7F, 0x7F, 0x00, 0x3C, 0x7F, 0x7F, 0x67, 0x00, 0x00, 0x00, 0x00,
};


const unsigned char PROGMEM menu_bitmap[] =
{
  //
  // ## ##  ### ##    ###
  // ## ## #### ##   #####
  // ##### ##   ##   ## ##
  // ##### #### ##   #####
  // ## ## ##   ##   ####
  // ## ## #### #### ##
  // ## ##  ###  ### ##
  //
  // ##   ###   ####  ####
  // ##  ##### ####  ######
  // ##  ## ## ##   ###  ###
  // ##  ## ## ###  ##    ##
  // ##  ## ## ###  ###  ###
  // ##  ## ## ##    ######
  // ##  ## ## ##     ####
  //
  //  ###   ####   ## ##  ###  ####
  // ####  ######  ## ## ##### #####
  // ##   ###  ### ## ## ## ## ##  ##
  //  ##  ##    ## ## ## ## ## ##  ##
  //   ## ###  ### ## ## ## ## ##  ##
  // ####  ######  ##### ## ## #####
  // ###    ####    ###  ## ## ####
  //
  //  ###  ##    ###  ##  ##
  // ##### ##   #####  ####
  // ## ## ##   ## ##   ##
  // ##### ##   #####   ##
  // ####  ##   #####   ##
  // ##    #### ## ##   ##
  // ##     ### ## ##   ##
  0xFE, 0xFE, 0x18, 0xFE, 0xFE, 0x00, 0x7C, 0xFE, 0xD6, 0xD6, 0x00, 0x7E, 0xFE, 0xC0, 0xC0, 0x00, 0xFC, 0xFE, 0x36, 0x3E, 0x1C, 0x00, 0x00, 0x00, 0x00, 0x00, 0x00, 0x00, 0x00, 0x00, 0x00, 0x00,
  0xFE, 0xFE, 0x00, 0x00, 0xFC, 0xFE, 0x06, 0xFE, 0xFC, 0x00, 0xFC, 0xFE, 0x36, 0x06, 0x02, 0x38, 0x7C, 0xEE, 0xC6, 0xC6, 0xEE, 0x7C, 0x38, 0x00, 0x00, 0x00, 0x00, 0x00, 0x00, 0x00, 0x00, 0x00,
  0xCC, 0xDE, 0xF6, 0x66, 0x00, 0x38, 0x7C, 0xEE, 0xC6, 0xC6, 0xEE, 0x7C, 0x38, 0x00, 0x7E, 0xFE, 0xC0, 0xFE, 0x7E, 0x00, 0xFC, 0xFE, 0x06, 0xFE, 0xFC, 0x00, 0xFE, 0xFE, 0xC6, 0xC6, 0x7C, 0x38,
  0xFC, 0xFE, 0x36, 0x3E, 0x1C, 0x00, 0x7E, 0xFE, 0xC0, 0xC0, 0x00, 0xFC, 0xFE, 0x36, 0xFE, 0xFC, 0x00, 0x02, 0x06, 0xFC, 0xFC, 0x06, 0x02, 0x00, 0x00, 0x00, 0x00, 0x00, 0x00, 0x00, 0x00, 0x00,
};

const unsigned char PROGMEM yes_bitmap[] =
{
  //
  // ##  ##  ###  ###
  //  ####  #### ####
  //   ##   ##   ##
  //   ##   ####  ##
  //   ##   ##     ##
  //   ##   #### ####
  //   ##    ### ###
  0x02, 0x06, 0xFC, 0xFC, 0x06, 0x02, 0x00, 0x7C, 0xFE, 0xD6, 0xD6, 0x00, 0xCC, 0xDE, 0xF6, 0x66,
};

const unsigned char PROGMEM no_bitmap[] =
{
  //
  //  ###    ####
  // #####  ######
  // ## ## ###  ###
  // ## ## ##    ##
  // ## ## ###  ###
  // ## ##  ######
  // ## ##   ####
  0xFC, 0xFE, 0x06, 0xFE, 0xFC, 0x00, 0x38, 0x7C, 0xEE, 0xC6, 0xC6, 0xEE, 0x7C, 0x38,
};


const unsigned char PROGMEM shade_bitmap[] =
{
  //  # # # # # # # # # # # # # # # #
  // # # # # # # # # # # # # # # # #
  //  # # # # # # # # # # # # # # # #
  // # # # # # # # # # # # # # # # #
  //  # # # # # # # # # # # # # # # #
  // # # # # # # # # # # # # # # # #
  //  # # # # # # # # # # # # # # # #
  // # # # # # # # # # # # # # # # #
  0xAA, 0x55, 0xAA, 0x55, 0xAA, 0x55, 0xAA, 0x55, 0xAA, 0x55, 0xAA, 0x55, 0xAA, 0x55, 0xAA, 0x55, 0xAA, 0x55, 0xAA, 0x55, 0xAA, 0x55, 0xAA, 0x55, 0xAA, 0x55, 0xAA, 0x55, 0xAA, 0x55, 0xAA, 0x55,
};


const unsigned char PROGMEM info_bitmap[] =
{
  //                                                                                                 
  //                                               ##               ##    #####     #####  #####   ##
  //                                               ##               ##   #######   ######  ######  ##
  //   ####     ####    ####    ######    ####     #####   ## ##    ##  ###   ###     ##   ##  ##  ##
  //  ######   ######  ######  ########  ######    ######  ## ##    ##  ##     ##   #####  ## ###  ##
  //  ##  ##   ##  ##  ##  ##  ## ## ##  ## ###    ##  ##  ## ##    ##  ##     ##      ##  ## ##   ##
  //  ##  ##   ##  ##  ##  ##  ## ## ##  ##        ##  ##  ## ##    ##  ###   ###      ##  ## ###  ##
  //  ######   ######  ######  ## ## ##  #####     ######  #####   ###   #######   ######  ##  ##  ##
  //   #####    #####   #####  ## ## ##   ####      ####    ####   ##     #####     ####   ##  ### ##
  //            #  ##                                        ###                                     
  //             ###                                       ####                                      
  //             ###                                       ###                                       
  //                                                                                                 
  //                 ##    ##       ##    ##               ##             ##                     ##  
  //                 ##    ##       ##    ##               ##             ##                    ###  
  //   ## ## ##  ##  ###   ####     ###   ####    ####     ####    ####   ##   ####      ####   ##   
  //   ## ## ##  ##  ###   #####    ###   #####  ######    #####  ######  ##  ######    ######  ##   
  //   ## ## ##  ##  ##    ## ##    ##    ## ##  ## ###    ## ##  ## ###  ##  ##  ##    ##  ##  ###  
  //   ## ## ##  ##  ####  ## ##    ####  ## ##  ##        ## ##  ##      ##  ##  ##    ##  ##  ###  
  //   ########  ##   ###  ## ##     ###  ## ##  #####     ## ##  #####   ##  ######    ######  ##   
  //    ######   ##    ##  ## ##      ##  ## ##   ####     ## ##   ####   ##  ####       ####   ##   
  //                                                                          ##                     
  //                            ######                  ##                    ##                     
  //                            ######                  ##                                           
  //                              ##    ##   ####     ####   ####     ##   ##                        
  //                              ##   ###  ######  ######  ######   ###  ###                        
  //                              ##   ##   ##  ##  ##  ##  ##  ##   ###  ###                        
  //                              ##   ##   ##  ##  ##  ##  ##  ##   ##   ##                         
  //                              ##   ##   ######  ######  ######  ###  ###                         
  //                              ##   ##    ####    ####    ####   ##   ##                          
  //                                                                                                 
  //                    ######                                                ####                   
  //                    #######                                               ####                   
  //                    ##   ###   ##   ####    ####    ######    ####    ##   ##                    
  //                    ##    ##  ###  ######  ######  ########  ######  ###  ####                   
  //                    ##    ##  ##   ## ###  ##  ##  ## ## ##  ## ###  ##     ##                   
  //                    ##   ###  ##   ##      ##  ##  ## ## ##  ##      ##     ##                   
  //                    ## ####   ##   #####   ######  ## ## ##  #####   ##   ####                   
  //                    ## ###    ##    ####    #####  ## ## ##   ####   ##   ###                    
  //                                                                                                 
  0x00, 0xF0, 0xF8, 0x98, 0x98, 0xF8, 0xF0, 0x00, 0x00, 0x00, 0xF0, 0xF8, 0x98, 0x98, 0xF8, 0xF0, 0x00, 0x00, 0xF0, 0xF8, 0x98, 0x98, 0xF8, 0xF0, 0x00, 0x00, 0xF0, 0xF8, 0x18, 0xF8, 0xF8, 0x18, 0xF8, 0xF0, 0x00, 0x00, 0xF0, 0xF8, 0x98, 0xB8, 0xB8, 0x30, 0x00, 0x00, 0x00, 0x00, 0xFE, 0xFE, 0x98, 0x98, 0xF8, 0xF0, 0x00, 0x00, 0xF8, 0xF8, 0x80, 0xF8, 0xF8, 0x00, 0x00, 0x00, 0x80, 0xFE, 0xFE, 0x00, 0x00, 0x78, 0xFC, 0xCE, 0x86, 0x86, 0x86, 0xCE, 0xFC, 0x78, 0x00, 0x00, 0x84, 0x96, 0x96, 0x9E, 0xFE, 0xF6, 0x00, 0x00, 0xFE, 0xFE, 0x06, 0x76, 0xFE, 0xDC, 0x00, 0x00, 0xFE, 0xFE, 
  0x00, 0x00, 0x81, 0x81, 0x01, 0x81, 0x81, 0x00, 0x80, 0x80, 0x00, 0x03, 0x8D, 0x8D, 0x0F, 0x03, 0xE0, 0xE0, 0x80, 0x01, 0x01, 0x01, 0xE1, 0xE1, 0x80, 0x80, 0x01, 0x01, 0x00, 0x01, 0x01, 0xE0, 0xE1, 0x81, 0x00, 0x00, 0x00, 0xE1, 0xE1, 0x81, 0x81, 0x00, 0x00, 0x00, 0x00, 0x80, 0x80, 0x81, 0x81, 0x01, 0x01, 0x00, 0x00, 0x00, 0xEC, 0xED, 0x8F, 0x87, 0x03, 0x00, 0x00, 0x00, 0x81, 0x81, 0x80, 0x80, 0x00, 0x00, 0x00, 0xE1, 0xE1, 0x01, 0x01, 0x01, 0x80, 0x80, 0x80, 0x80, 0x00, 0x01, 0x01, 0x01, 0x01, 0x00, 0x80, 0x80, 0x81, 0x81, 0x00, 0x00, 0x01, 0xC1, 0xE1, 0x60, 0x01, 0x01, 
  0x00, 0x00, 0x0F, 0x1F, 0x18, 0x1F, 0x1F, 0x18, 0x1F, 0x0F, 0x00, 0x00, 0x1F, 0x1F, 0x00, 0x00, 0x07, 0x0F, 0x1D, 0x1C, 0x00, 0x00, 0x1F, 0x1F, 0x01, 0x1F, 0x1F, 0xC0, 0xC0, 0xC0, 0xC0, 0xC7, 0xCF, 0x1D, 0x1C, 0x00, 0x00, 0x1F, 0x1F, 0x01, 0x1F, 0x1F, 0x00, 0x00, 0x0F, 0x1F, 0x19, 0x1B, 0x1B, 0x03, 0x00, 0xC0, 0xC0, 0x00, 0x1F, 0x1F, 0x01, 0x1F, 0x1F, 0x00, 0x00, 0x0F, 0x1F, 0x19, 0x1B, 0x1B, 0x03, 0x00, 0x00, 0x1F, 0x1F, 0x00, 0x00, 0x7F, 0x7F, 0x19, 0x19, 0x0F, 0x0F, 0x00, 0x00, 0x00, 0x00, 0x0F, 0x1F, 0x19, 0x19, 0x1F, 0x0F, 0x00, 0x00, 0x1F, 0x1F, 0x06, 0x00, 0x00, 
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
};


const unsigned char PROGMEM pause_bitmap[] =
{
  //
  //     # #         # # #     # #   # #       # #     # # #
  //    # # #       # # # #   # #     # #     # #     # # # #
  //   # # # #     # # # #     # #   # #     # # #   # # # #
  //  # # # # #   # # # # #   # #     # #   # # #   # # # # #
  // # #     # # # #     # #   # #   # #     # #     # #
  //  # #   # #   # #   # #   # #     # #   # # #   # #
  // # #   # # # # #     # #   # #   # #     # #     # # # #
  //  # # # # #   # #   # #   # #     # #   # # #   # # # #
  // #### #####  ###### ####  ####   ####    #####  ########
  // #### ####   ###### ####  ####   ####    #####  ########
  // ####        ###### ####  ####   ####    #####  ####
  // ####        ###### ####  ###########   ######  #########
  // ####        ####   ####   #########   ######    ########
  // ####        ####   ####    #######    ######     #######
  // ####        ####   ####     #####     ####        #####
  0xA0, 0x50, 0xA8, 0x54, 0x0A, 0x14, 0x8A, 0x54, 0xA8, 0x50, 0xA0, 0x00, 0xA0, 0x50, 0xA8, 0x54, 0x0A, 0x14, 0x0A, 0x54, 0xAA, 0x54, 0xA0, 0x00, 0x00, 0x54, 0xAA, 0x54, 0xAA, 0x00, 0x00, 0x00, 0xAA, 0x54, 0xAA, 0x54, 0x00, 0x00, 0x00, 0x50, 0xA8, 0x54, 0xAA, 0x54, 0x0A, 0x00, 0x00, 0x50, 0xA8, 0x54, 0xAA, 0x14, 0x8A, 0x14, 0x8A, 0x14,
  0xFE, 0xFF, 0xFE, 0xFF, 0x00, 0x07, 0x06, 0x07, 0x06, 0x03, 0x00, 0x00, 0xFE, 0xFF, 0xFE, 0xFF, 0x1E, 0x1E, 0x00, 0xFF, 0xFE, 0xFF, 0xFE, 0x00, 0x00, 0x1F, 0x3E, 0x7F, 0xFE, 0xF0, 0xF0, 0xF0, 0xFE, 0x7F, 0x3E, 0x1F, 0x00, 0x00, 0xE0, 0xF1, 0xFE, 0xFF, 0x7E, 0x7F, 0x1E, 0x00, 0x00, 0x1F, 0x3E, 0x7F, 0xFE, 0xF7, 0xF6, 0xF7, 0xF6, 0x70,
};

const unsigned char PROGMEM gameover_bitmap[] =
{
  //
  //          # # #         # # #       # # #   # # #       # # #
  //       # # # #         # # # #     # # # # # # # #     # # # #
  //      # # # # #       # # # # #   # # # # # # # # #   # # # #
  //     # # # # #       # # # # # #   # # # # # # # #   # # # # #
  //      # #     #     # # #   # #   # #   # #     # #   # #
  //     # #             # #     # #   # #   # #   # #   # #
  //    # #             # #     # #   # #   # #     # #   # # # #
  //     # #     # #     # #     # #   # #   # #   # #   # # # # #
  //    # #     # # #   # # #   # #   # #   # #     # #   # # # #
  //     # #     # # #   # # #   # #   # #   # #   # #   # # # # #
  //    # # #   # # #   # # #   # #
  //     # # #     # #   # # #   #  #####   ### ###  ### #####
  //      # # # # # #   # #     #  #######  ######  #### ###### #
  //       # # # # #     # #      ###   ###  #####  ##   ##  ##  #
  //        # # # #     # #     # ##  #  ##  ####   #### ## ### #
  //         # # #       # #      ##     ##  ####   #### ## ##   #
  //                              ###   ###   ##    ##   ## ###
  //                               #######    ##    #### ##  ##
  //                                #####     #      ### ##  ###
  //
  //
  //
  //
  0x00, 0x00, 0x00, 0x80, 0x50, 0xA8, 0x54, 0x28, 0x14, 0x0A, 0x14, 0x0A, 0x14, 0x2A, 0x00, 0x00, 0x00, 0x00, 0x00, 0xA0, 0x50, 0xA8, 0x54, 0x2A, 0x14, 0x0A, 0x14, 0xAA, 0x54, 0xA8, 0x50, 0x00, 0x00, 0xA8, 0x54, 0xAA, 0x54, 0x0A, 0x14, 0xAA, 0x54, 0xA8, 0x54, 0x0A, 0x14, 0x0A, 0x54, 0xAA, 0x54, 0xA8, 0x00, 0x00, 0x50, 0xA8, 0x54, 0xAA, 0x14, 0x8A, 0x14, 0x8A, 0x14, 0x00, 0x00, 0x00,
  0x00, 0x00, 0x00, 0x0A, 0x15, 0x2A, 0x55, 0xA8, 0x50, 0xA0, 0x40, 0xAA, 0x45, 0xAA, 0x55, 0x2A, 0x14, 0x00, 0x00, 0xAA, 0x55, 0xAA, 0x55, 0x0A, 0x14, 0x00, 0x00, 0xAA, 0x15, 0xCA, 0xE5, 0x70, 0x30, 0xB2, 0x35, 0x72, 0xE5, 0xC0, 0x00, 0x32, 0xF5, 0xF2, 0xE5, 0xF0, 0x70, 0x10, 0x05, 0xE2, 0xF5, 0xB2, 0xB0, 0x00, 0xF5, 0xF2, 0x35, 0xB2, 0xF5, 0xE2, 0x05, 0xA2, 0x45, 0x00, 0x00, 0x00,
  0x00, 0x00, 0x00, 0x00, 0x00, 0x00, 0x00, 0x00, 0x01, 0x00, 0x01, 0x00, 0x01, 0x00, 0x00, 0x00, 0x00, 0x00, 0x00, 0x00, 0x01, 0x00, 0x01, 0x00, 0x00, 0x00, 0x00, 0x00, 0x00, 0x03, 0x07, 0x0E, 0x0C, 0x0C, 0x0C, 0x0E, 0x07, 0x03, 0x00, 0x00, 0x01, 0x0F, 0x07, 0x01, 0x00, 0x00, 0x00, 0x07, 0x0F, 0x0D, 0x0D, 0x00, 0x0F, 0x0F, 0x00, 0x03, 0x0F, 0x0E, 0x08, 0x00, 0x01, 0x00, 0x00, 0x00,
};

const unsigned char PROGMEM score_bitmap[] =
{
  //
  //    #### #### #### ###  ####
  //    #    #    #  # #  # #    #
  //    #### #    #  # #  # ##
  //       # #    #  # ###  #
  //    #### #### #### #  # #### #
  //    #### #### #### #  # #### #
  //
  0x00, 0x00, 0x00, 0x6E, 0x6A, 0x6A, 0x7A, 0x00, 0x7E, 0x62, 0x62, 0x62, 0x00, 0x7E, 0x62, 0x62, 0x7E, 0x00, 0x7E, 0x12, 0x12, 0x6C, 0x00, 0x7E, 0x6A, 0x62, 0x62, 0x00, 0x64, 0x00, 0x00, 0x00,
};

const unsigned char PROGMEM candletip_bitmap[] =
{
  //           ####
  //       ## ######
  //    ############
  //   #############
  //  ##############
  // ###############
  // ###############
  // ###############
  // ###############
  // ###############
  // ###############
  // # #############
  // # #############
  // # #############
  // # #############
  //   #############
  //   #############
  //   ############
  //   ############
  //   ############
  //   ############
  //   ############
  //   ############
  //   ############
  //   ############
  //   ############
  //   ############
  //   ############
  //   ############
  //   ############
  //   ############
  //   ############
  0xE0, 0xF0, 0xF8, 0xFC, 0xFC, 0xFC, 0xFE, 0xFE, 0xFC, 0xFE, 0xFF, 0xFF, 0xFF, 0xFF, 0xFE, 0x00,
  0x7F, 0x07, 0xFF, 0xFF, 0xFF, 0xFF, 0xFF, 0xFF, 0xFF, 0xFF, 0xFF, 0xFF, 0xFF, 0xFF, 0xFF, 0x00,
  0x00, 0x00, 0xFF, 0xFF, 0xFF, 0xFF, 0xFF, 0xFF, 0xFF, 0xFF, 0xFF, 0xFF, 0xFF, 0xFF, 0x01, 0x00,
  0x00, 0x00, 0xFF, 0xFF, 0xFF, 0xFF, 0xFF, 0xFF, 0xFF, 0xFF, 0xFF, 0xFF, 0xFF, 0xFF, 0x00, 0x00,
};

const unsigned char PROGMEM life_bitmap[] =
{
  //        #    # #### ####
  //   #### #    # #    #
  //   #    #    # ###  ####
  // #####  #    # #    #
  //  ###   #### # #    ####
  //   #    #### # #    ####
  0x08, 0x18, 0x3E, 0x1A, 0x0A, 0x02, 0x00, 0x3F, 0x30, 0x30, 0x30, 0x00, 0x3F, 0x00, 0x3F, 0x05, 0x05, 0x01, 0x00, 0x3F, 0x35, 0x35, 0x35, 0x00,
};
