lmayencourt/faboy/software/game/ECOMD_AB_v10/ECOMD_AB_v10/score.h

#ifndef SCORE_H
#define SCORE_H


//define score font size
#define SCORE_SMALL_FONT          0
#define SCORE_BIG_FONT            1

PROGMEM const unsigned char numbersSmall[] = {
// width, height
3, 8,
// frame 0
0x1F, 0x11, 0x1F, 
// frame 1
0x12, 0x1F, 0x10, 
// frame 2
0x1D, 0x15, 0x17, 
// frame 3
0x11, 0x15, 0x1F, 
// frame 4
0x07, 0x04, 0x1F, 
// frame 5
0x17, 0x15, 0x1D, 
// frame 6
0x1F, 0x15, 0x1D, 
// frame 7
0x01, 0x01, 0x1F, 
// frame 8
0x1F, 0x15, 0x1F, 
// frame 9
0x17, 0x15, 0x1F, 
};


PROGMEM const unsigned char numbersBig[] = {
// width, height
18, 32,
// frame 0
0x40, 0xE0, 0x98, 0xFC, 0xFC, 0xF4, 0x1C, 0x1C, 0x14, 0x14, 
0x7C, 0xF4, 0xFE, 0xF5, 0xD8, 0x08, 0x00, 0x00, 0x00, 0xF8, 
0xBF, 0xFF, 0xFF, 0xEF, 0x00, 0x00, 0x00, 0x02, 0x71, 0xEB, 
0xFF, 0xFF, 0xFE, 0x8E, 0x80, 0x00, 0x02, 0x19, 0xFE, 0xFF, 
0xFF, 0xFF, 0x00, 0x00, 0x00, 0x00, 0x6F, 0xDF, 0xFF, 0xFF, 
0xFF, 0x00, 0x00, 0x00, 0x00, 0x28, 0x7F, 0x5F, 0x7F, 0x1F, 
0x78, 0x68, 0x70, 0x71, 0x61, 0xF5, 0xBF, 0x7F, 0x27, 0x18, 
0x00, 0x00, 
// frame 1
0x00, 0x00, 0x00, 0x00, 0x10, 0x1C, 0xFE, 0xFE, 0xFE, 0xEE, 
0x78, 0xE0, 0x90, 0x00, 0x00, 0x00, 0x00, 0x00, 0x00, 0x00, 
0x00, 0x00, 0x40, 0x20, 0xFF, 0xFF, 0xFF, 0xFF, 0xEF, 0x00, 
0x18, 0x00, 0x00, 0x00, 0x00, 0x00, 0x00, 0x00, 0x00, 0x00, 
0x00, 0x20, 0xFF, 0xFF, 0xFF, 0xFB, 0xF3, 0x0C, 0x88, 0x00, 
0x00, 0x00, 0x00, 0x00, 0x00, 0x00, 0x00, 0x00, 0x20, 0x83, 
0x3F, 0x7F, 0x7F, 0x7F, 0x3F, 0x25, 0x06, 0x44, 0x00, 0x00, 
0x00, 0x00, 
// frame 2
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
        sprites.drawSelfMasked(scoreX + (20 * i), scoreY, numbersBig, 0);
        break;
    }
  }

  for (byte i = 0; i < charLen; i++)
  {
    char digit = buf[i];
    byte j;
    if (digit <= 48)
    {
      digit = 0;
    }
    else {
      digit -= 48;
      if (digit > 9) digit = 0;
    }

    for (byte z = 0; z < 10; z++)
    {
      if (digit == z) j = z;
    }
    switch (fontType)
    {
      case SCORE_SMALL_FONT:
        sprites.drawSelfMasked(scoreX + (pad * 4) + (4 * i), scoreY, numbersSmall, digit);
        break;
      case SCORE_BIG_FONT:
        sprites.drawSelfMasked(scoreX + (pad * 20) + (20 * i), scoreY, numbersBig, digit);
        break;
    }
  }
}

#endif
