lmayencourt/faboy/software/game/sudoku_AB_v11-master/sudoku_AB_v11/puzzles.h

/* Neil Pierson - June 11, 2016
 *
 * puzzles.h
 *
 * Solve Sudoku Puzzles
 *  http://www.sudoku.com/
 *
 * Complete a 9x9 grid so that every row, column and 3x3 box contains
 * the numbers 1 through 9 (no repeats).
 *
 * Input puzzle can be defined by 9 long (32bit) integers (36 bytes, best compact form, more efficient than 9 nibbles)
 * Each integer should be 9 numbers long. Use 0's for empty/unknown numbers.
 * (drop leading 0s to avoid octal interpretation)
 *
 * Example:  12345060,         0, 450600037,   8030400,   7090500,   5010600, 590002041,         0,  30459780
 *
 * defines input puzzle:
 *
 *          +-----+-----+-----+
 *          |  1 2|3 4 5|  6  |
 *          |     |     |     |
 *          |4 5  |6    |  3 7|
 *          +-----+-----+-----+
 *          |    8|  3  |4    |
 *          |    7|  9  |5    |
 *          |    5|  1  |6    |
 *          +-----+-----+-----+
 *          |5 9  |    2|  4 1|
 *          |     |     |     |
 *          |  3  |4 5 9|7 8  |
 *          |-----+-----+-----+
 *
 * Puzzles from "The Big Book of Su Doku #1" by Mark Huckvale (2005)
 * Published by Newmarket Press, ISBN 1-55704-703-0
 * https://us.nicebooks.com/book/17516304
 */

#define PUZZLES    45 // total number of puzzles
#define PZ_MEDIUM  15 // first Medium puzzle (index)
#define PZ_HARD    25 // first   Hard puzzle (index)
#define PZ_CUSTOM 255 // custom puzzle, loaded from Serial input

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
      20001,  10008309,   6000040, 709003000,  30000010,    700508,  40000700, 203900060, 100070000, //  6 prunes
    1020000, 300456000, 726000000, 405010000, 803000906,     80407,       368,    269004,     30100, // 25 prunes
   12345060,         0, 450600037,   8030400,   7090500,   5010600, 590002041,         0,  30459780, // 40 prunes
  // http://puzzling.stackexchange.com/questions/12/are-there-sudoku-puzzles-published-that-do-require-guessing
  671000523, 493000187, 285371900,   6800710, 907050608,  48007200,   2749800, 859000471, 764000392, //  2 guesses (1 dead-end)
      64203,  40008906,   6050407, 603800745, 450603821,    540639, 201430508, 704105362,         0, //  1 guess
  140900730, 763014800,   2030461,  37001600,  50000140,   1000250, 810040900, 329100504,  74009310, //  2 guesses (1 dead-end)
    2500098, 490020005, 305900200, 864312759, 153798020, 927654831, 201005903,     30582, 530200100, //  2 guesses (1 dead-end)
  // http://www.sudokudragon.com/sudokuguess.htm
          3,    800140, 560090200, 941005300,     40000,   3100459,   7030018,  38006000, 400000000  //  2 guesses (1 dead-end)
   
};
