lmayencourt/faboy/software/game/SHRUN-AB_v15/SHRUN-AB_v15/numberbitmaps.h

const unsigned char PROGMEM number0_bitmap[] =
{
  //
  //  ##
  // #  #
  // #  #
  // #  #
  // #  #
  //  ##
  //
  0x3C, 0x42, 0x42, 0x3C, 0x00, 0x00, 0x00, 0x00,
  };
  const unsigned char PROGMEM number1_bitmap[] =
{
  //
  //  ##
  // # #
  //   #
  //   #
  //   #
  // ####
  //
  0x44, 0x42, 0x7E, 0x40, 0x00, 0x00, 0x00, 0x00,
  };
  const unsigned char PROGMEM number2_bitmap[] =
{
  //
  //  ###
  // #  #
  //    #
  //   #
  //  #
  // ####
  //
  0x44, 0x62, 0x52, 0x4E, 0x00, 0x00, 0x00, 0x00,
  };
  const unsigned char PROGMEM number3_bitmap[] =
{
  //
  //  ###
  // #  #
  //  ###
  //    #
  // #  #
  // ###
  //
  0x64, 0x4A, 0x4A, 0x3E, 0x00, 0x00, 0x00, 0x00,
  };
  const unsigned char PROGMEM number4_bitmap[] =
{
  //
  //   #
  // ###
  // # #
  // ####
  //   #
  //   #
  //
  0x1C, 0x14, 0x7E, 0x10, 0x00, 0x00, 0x00, 0x00,
  };
  const unsigned char PROGMEM number5_bitmap[] =
{
  //
  //  ###
  // ##
  //   #
  //   #
  // # #
  // ##
  //
  0x64, 0x46, 0x3A, 0x02, 0x00, 0x00, 0x00, 0x00,
  };
  const unsigned char PROGMEM number6_bitmap[] =
{
  //
  //   ##
  //  #
  // ####
  // #  #
  // #  #
  //  ##
  //
  0x38, 0x4C, 0x4A, 0x3A, 0x00, 0x00, 0x00, 0x00,
  };
  const unsigned char PROGMEM number7_bitmap[] =
{
  //
  // ####
  // #  #
  //   #
  //   #
  //   #
  //  #
  //
  0x06, 0x42, 0x3A, 0x06, 0x00, 0x00, 0x00, 0x00,
  };
  const unsigned char PROGMEM number8_bitmap[] =
{
  //
  // ####
  // #  #
  //  ##
  // #  #
  // #  #
  // ###
  //
  0x76, 0x4A, 0x4A, 0x36, 0x00, 0x00, 0x00, 0x00,
  };
  const unsigned char PROGMEM number9_bitmap[] =
{
  //
  // ####
  // #  #
  //  ###
  //    #
  //    #
  // ###
  //
  0x46, 0x4A, 0x4A, 0x3E, 0x00, 0x00, 0x00, 0x00,
};

const unsigned char *number_bitmaps[] = {number0_bitmap, number1_bitmap, number2_bitmap, number3_bitmap, number4_bitmap, number5_bitmap, number6_bitmap, number7_bitmap, number8_bitmap, number9_bitmap};
